tylerTaerak/ArduinoProject_3_Axis_Motion/SolidWorks_Parts/Axis.SLDPRT

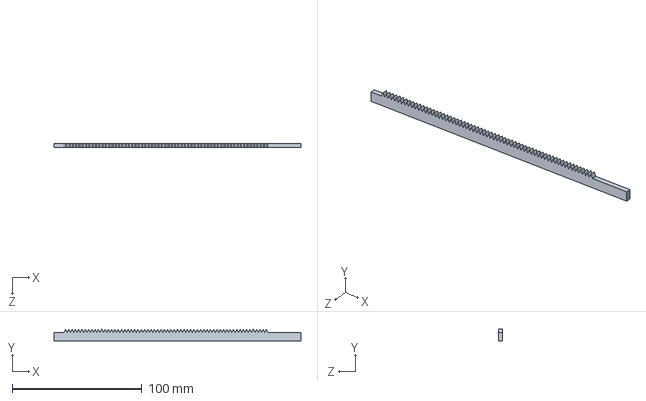
[picture p17: CAD file, 2021-08-22]
SolidWorks_Parts/Axis.SLDPRT
190.5 x 8.89 x 3.17 mm
