tylerTaerak/ArduinoProject_3_Axis_Motion/SolidWorks_Parts/MovingPart.SLDPRT

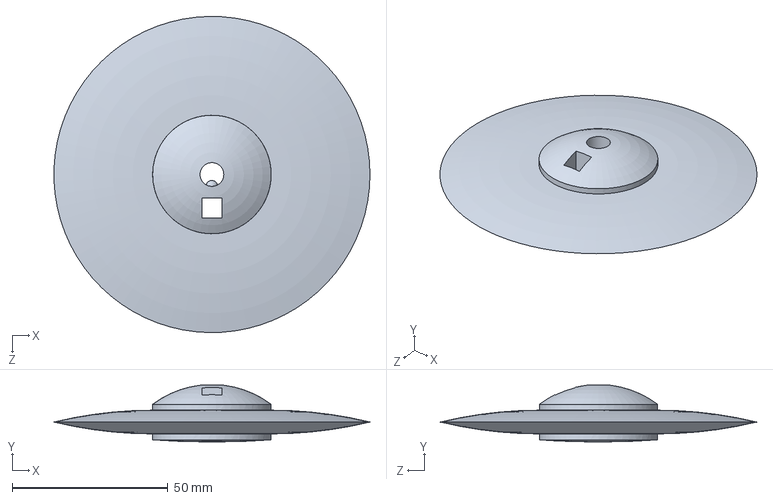
[picture p18: CAD file, 2021-08-22]
SolidWorks_Parts/MovingPart.SLDPRT
101.6 x 18.2 x 101.6 mm
