tylerTaerak/ArduinoProject_3_Axis_Motion/SolidWorks_Parts/ZStabilizer.SLDPRT

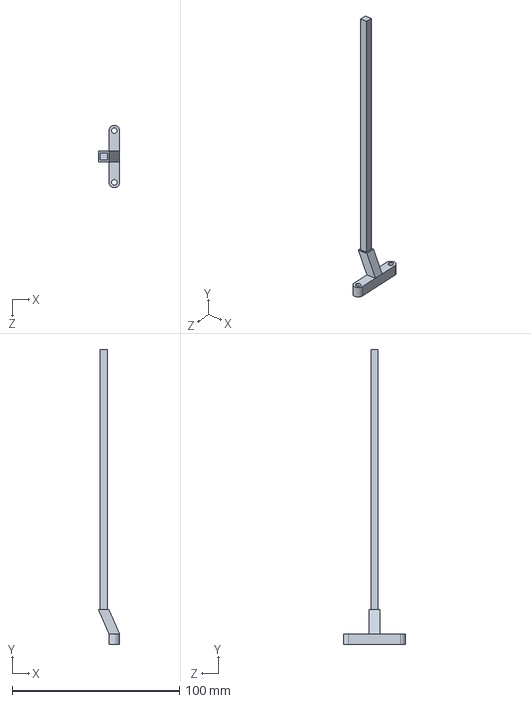
[picture p19: CAD file, 2021-08-22]
SolidWorks_Parts/ZStabilizer.SLDPRT
12.7 x 176.4 x 37.3 mm
